BegoonLab/xiao-esp32c6-wifi-sensor/main/sensor_gpio.c

/**
 * @file    sensor_gpio.c
 * @author  Alexander Begoon <alex@begoonlab.tech>
 * @date    28 September 2024
 * @brief   //TODO
 *
 * @details //TODO
 *
 * @copyright Copyright (c) 2024 <a href="https://begoonlab.tech">BegoonLab</a>.
 *            All rights reserved.
 */

#include "sensor_gpio.h"

enum { LOW = 0, HIGH = 1 };

void init_gpio(void) {
#if defined(CONFIG_WIFI_ANTENNA_EXTERNAL) ||                                   \
    defined(CONFIG_ZIGBEE_ANTENNA_EXTERNAL)
  gpio_reset_pin(GPIO_NUM_3);
  gpio_set_direction(GPIO_NUM_3, GPIO_MODE_OUTPUT);
  gpio_set_level(GPIO_NUM_3, LOW);

  gpio_reset_pin(GPIO_NUM_14);
  gpio_set_direction(GPIO_NUM_14, GPIO_MODE_OUTPUT);
  gpio_set_level(GPIO_NUM_14, HIGH);
#endif
}
